Fabiancrg/Aeris_Lite/main/esp_zb_aeris.h

/*
 * Zigbee Aeris Air Quality Sensor Header
 */

#ifndef ESP_ZB_AERIS_H
#define ESP_ZB_AERIS_H

#include "esp_zigbee_core.h"
#include "aeris_driver.h"
#include "zcl_utility.h"

/* Zigbee configuration */
#define INSTALLCODE_POLICY_ENABLE       false                                /* enable the install code policy for security */
#define ED_AGING_TIMEOUT                ESP_ZB_ED_AGING_TIMEOUT_64MIN        /* aging timeout of device */
#define ED_KEEP_ALIVE                   3000                                 /* 3000 millisecond */

/* Air Quality Sensor Endpoints */
#define HA_ESP_TEMP_HUM_ENDPOINT        1                                    /* Temperature and Humidity sensor endpoint */
#define HA_ESP_PRESSURE_ENDPOINT        2                                    /* Pressure sensor endpoint */
#define HA_ESP_VOC_ENDPOINT             3                                    /* VOC Index sensor endpoint */
#define HA_ESP_NOX_ENDPOINT             4                                    /* NOx Index sensor endpoint */
#define HA_ESP_CO2_ENDPOINT             5                                    /* CO2 sensor endpoint */
#define HA_ESP_LED_CONFIG_ENDPOINT      6                                    /* LED configuration endpoint */
#define HA_ESP_STATUS_LED_ENDPOINT      7                                    /* Zigbee status LED endpoint */

/* Custom attribute IDs for LED thresholds (manufacturer-specific range 0xF000-0xFFFF) */
#define ZCL_LED_ATTR_VOC_ORANGE         0xF000
#define ZCL_LED_ATTR_VOC_RED            0xF001
#define ZCL_LED_ATTR_NOX_ORANGE         0xF002
#define ZCL_LED_ATTR_NOX_RED            0xF003
#define ZCL_LED_ATTR_CO2_ORANGE         0xF004
#define ZCL_LED_ATTR_CO2_RED            0xF005
#define ZCL_LED_ATTR_HUM_ORANGE_LOW     0xF006
#define ZCL_LED_ATTR_HUM_ORANGE_HIGH    0xF007
#define ZCL_LED_ATTR_HUM_RED_LOW        0xF008
#define ZCL_LED_ATTR_HUM_RED_HIGH       0xF009
#define ZCL_LED_ATTR_PM25_ORANGE        0xF00A
#define ZCL_LED_ATTR_PM25_RED           0xF00B
#define ZCL_LED_ATTR_ENABLE_MASK        0xF00C  // Bitmask for individual LED control
#define ZCL_LED_ATTR_PM_POLL_INTERVAL   0xF00D  // PM sensor polling interval in seconds (0=continuous)
#define ZCL_LED_ATTR_BRIGHTNESS         0xF00E  // LED brightness level (0-255)
#define ZCL_ATTR_TEMP_OFFSET            0xF00F  // Temperature offset in 0.1°C (signed int16, e.g., 30 = 3.0°C)
#define ZCL_ATTR_HUMIDITY_OFFSET        0xF010  // Humidity offset in 0.1% (signed int16, e.g., 10 = 1.0%)
#define ZCL_ATTR_REFRESH_INTERVAL       0xF011  // Sensor refresh interval in seconds (10-3600)

#define ESP_ZB_PRIMARY_CHANNEL_MASK     ESP_ZB_TRANSCEIVER_ALL_CHANNELS_MASK /* Zigbee primary channel mask use in the example */

/* Button configuration */
#define ESP_INTR_FLAG_DEFAULT 0

/* Basic manufacturer information */
#define ESP_MANUFACTURER_NAME "\x09""ESPRESSIF"      /* Customized manufacturer name */
#define ESP_MODEL_IDENTIFIER "\x07""aeris-z"         /* Air quality sensor model */

/* Router configuration (was ZED_CONFIG - changed to match working example) */
#define ESP_ZB_ROUTER_CONFIG()                                      \
    {                                                               \
        .esp_zb_role = ESP_ZB_DEVICE_TYPE_ROUTER,                   \
        .install_code_policy = INSTALLCODE_POLICY_ENABLE,           \
        .nwk_cfg = {                                                \
            .zczr_cfg = {                                           \
                .max_children = 10,                                 \
            },                                                      \
        },                                                          \
    }

/* Legacy ZED config kept for reference (not used) */
#define ESP_ZB_ZED_CONFIG()                                         \
    {                                                               \
        .esp_zb_role = ESP_ZB_DEVICE_TYPE_ED,                       \
        .install_code_policy = INSTALLCODE_POLICY_ENABLE,           \
        .nwk_cfg.zed_cfg = {                                        \
            .ed_timeout = ED_AGING_TIMEOUT,                         \
            .keep_alive = ED_KEEP_ALIVE,                            \
        },                                                          \
    }

#define ESP_ZB_DEFAULT_RADIO_CONFIG()                           \
    {                                                           \
        .radio_mode = ZB_RADIO_MODE_NATIVE,                     \
    }

#define ESP_ZB_DEFAULT_HOST_CONFIG()                            \
    {                                                           \
        .host_connection_mode = ZB_HOST_CONNECTION_MODE_NONE,   \
    }

#endif
